Natchpai/LQRx_InterleavedBuck/Images/GCM155R71H104KE02J-100nF50V.png

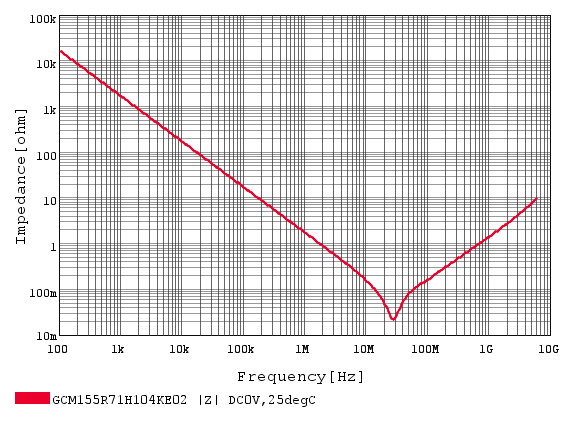
Images/GCM155R71H104KE02J-100nF50V.png
