Natchpai/LQRx_InterleavedBuck/Images/GRM21BZ71E475KE15L-4u7F25V-Derating.png

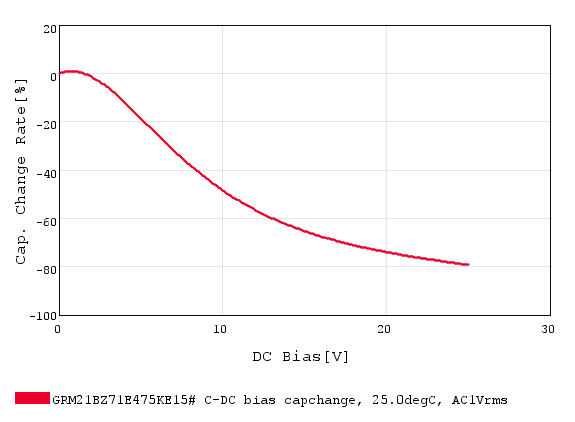
Images/GRM21BZ71E475KE15L-4u7F25V-Derating.png
