Natchpai/LQRx_InterleavedBuck/Images/GRM31CR71H475KA12L-4u7F50V_Z.png

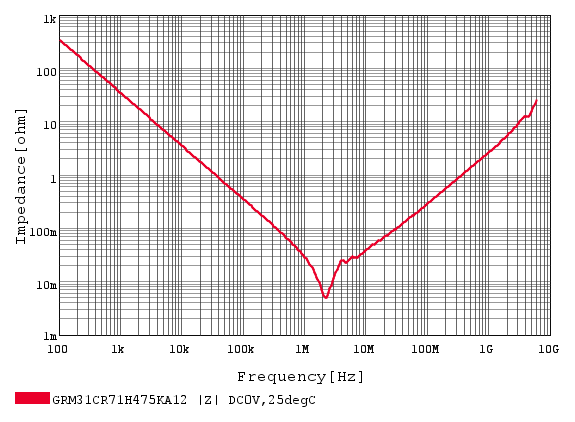
Images/GRM31CR71H475KA12L-4u7F50V_Z.png
