Natchpai/LQRx_InterleavedBuck/Images/GRM155R71E103KA01D.png

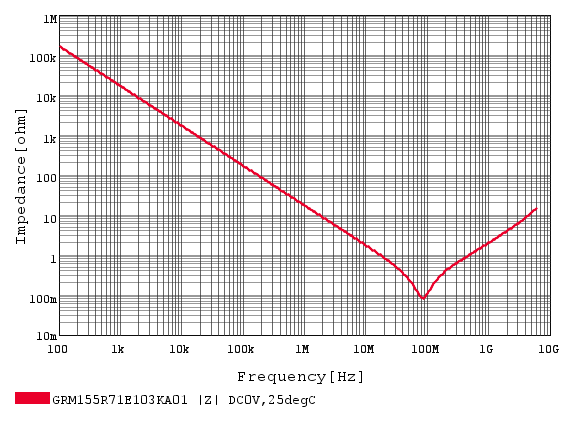
Images/GRM155R71E103KA01D.png
