Natchpai/LQRx_InterleavedBuck/Images/Render-Board/2Phase_SynchBuck_Bottomview_v1-1 (Large).png

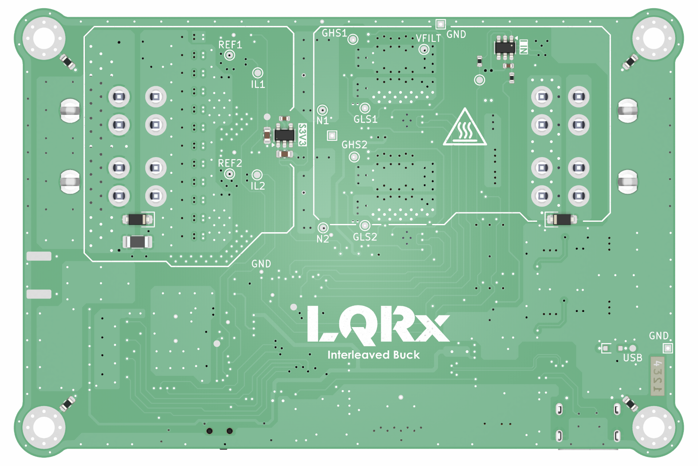
Images/Render-Board/2Phase_SynchBuck_Bottomview_v1-1 (Large).png
