Natchpai/LQRx_InterleavedBuck/Simulation/LC_Filter.asc

C1: cap; {Cd}
C2: cap; {Cf}
C3: cap; 0.1µ
C4: cap; {Cf}
C5: cap; 0.1µ
C6: cap; 10p
C7: cap; 10p
C8: cap; {Cd}
C9: cap; 2µ
C10: cap; {Cd}
C11: cap; 0.1µ
C12: cap; 0.1µ
C13: cap; 10p
C14: cap; 10p
C15: cap; {Cd}
C16: cap; 2µ
C17: cap; {Cd}
C18: cap; {Cf}
C19: cap; 0.1µ
C20: cap; 0.1µ
C21: cap; 10p
C22: cap; 10p
C23: cap; {Cf}
C24: cap; {Ci}; Lser=200p
C25: cap; 47µ; Rser=10m Lser=2n
C26: cap; 47µ
C27: cap; 47µ; Rser=10m Lser=2n
C28: cap; {Ci}; Lser=200p
C29: cap; {Ci}; Lser=200p
C30: cap; {Ci}; Lser=200p
C31: cap; {Ci}; Lser=200p
C32: cap; {Ci}; Lser=200p
C33: cap; 0.1µ; Lser=200p
C34: cap; 0.1µ; Lser=200p
C35: cap; {Ci}; Lser=200p
C36: cap; 47µ; Lser=3n
C37: cap; 47µ; Lser=3n
C38: cap; 47µ; Lser=3n
C39: cap; 0.1µ; Lser=200p
C40: cap; 0.1µ; Lser=200p
C41: cap; {Ci}; Lser=200p
C42: cap; {Ci}; Lser=200p
C43: cap; {Ci}; Lser=200p
C44: cap; {Ci}; Lser=200p
C45: cap; {Ci}; Lser=200p
C46: cap; {Ci}; Lser=200p
C47: cap; {Ci}; Lser=200p
C48: cap; {Ci}; Lser=200p
C49: cap; {Ci}; Lser=200p
C50: cap; 47µ; Lser=3n
C51: cap; 47µ; Lser=3n
C52: cap; 47µ; Lser=3n
C53: cap; 0.1µ; Lser=200p
C54: cap; 0.1µ; Lser=200p
C55: cap; {Ci}; Lser=200p
C56: cap; {Ci}; Lser=200p
C57: cap; {Ci}; Lser=200p
C58: cap; {Ci}; Lser=200p
C59: cap; {Ci}; Lser=200p
C60: cap; {Ci}; Lser=200p
C61: cap; {Ci}; Lser=200p
C62: cap; {Ci}; Lser=200p
C63: cap; {Ci}; Lser=200p
C64: cap; {Ci}; Lser=200p
C65: cap; {Ci}; Lser=200p
C66: cap; {Ci}; Lser=200p
C67: cap; {Ci}; Lser=200p
C68: cap; {Ci}; Lser=200p
I1: current; ""; AC 1
I2: current; ""; AC 1
I3: current; ""; AC 1
I4: current; ""; AC 1
L1: ind; 1µ; Rser=1m
L2: ind; 1µ; Rser=1m
L3: ind; 250p; Rser=1m
L4: ind; 250p; Rser=1m
L5: ind; 5n; Rser=1m
L6: ind; 250p; Rser=1m
L7: ind; 250p; Rser=1m
L8: ind; 1µ; Rser=1m
L9: ind; 1µ; Rser=1m
L10: ind; 5n; Rser=1m
L11: ind; 250p; Rser=1m
L12: ind; 1µ; Rser=1m
L13: ind; 250p; Rser=1m
L14: ind; 250p; Rser=1m
L15: ind; 5n; Rser=1m
L16: ind; 1µ; Rser=1m
L17: ind; 5n; Rser=1m
L18: ind; 5n; Rser=1m
L19: ind; 250p; Rser=1m
L20: ind; 250p; Rser=1m
L21: ind; 250p; Rser=1m
L22: ind; 250p; Rser=1m
L23: ind; 250p; Rser=1m
L24: ind; 1µ; Rser=1m
L25: ind; 1µ; Rser=1m
L26: ind; 1µ; Rser=1m
R1: res; 6m
R2: res; {Rd}
R3: res; 2m
R4: res; 6m
R5: res; 0.01
R6: res; 2m
R7: res; 0.01
R8: res; 6m
R9: res; 6m
R10: res; 2m
R11: res; 6m
R12: res; 2m
R13: res; 0.01
R14: res; 0.01
R15: res; {Zin}
R16: res; {Rd}
R17: res; {Rd}
R18: res; {Rd}
R19: res; {Rd}
R20: res; 6m
R21: res; 2m
R22: res; 0.01
R23: res; 0.01
R24: res; 2m
R25: res; 0.4
R26: res; 4m
R27: res; 0.5
R28: res; 5.6m
R29: res; 5m
R30: res; 0.4
R31: res; 1m
R32: res; 1m
R33: res; 1m
R34: res; 1m
R35: res; 4m
R36: res; 4m
R37: res; 4m
R38: res; 1m
R39: res; 1m
R40: res; 4m
R41: res; 4m
R42: res; 2m
R43: res; 2m
R44: res; 0.4
R45: res; 4m
R46: res; 0.4
R47: res; 5.6m
R48: res; 5m
R49: res; 0.4
R50: res; 1m
R51: res; 1m
R52: res; 1m
R53: res; 1m
R54: res; 4m
R55: res; 4m
R56: res; 4m
R57: res; 1m
R58: res; 1m
R59: res; 4m
R60: res; 4m
R61: res; 2m
R62: res; 2m
R63: res; 4m
R64: res; 4m
R65: res; 4m
R66: res; 4m
R67: res; 0.4
R68: res; 0.4
R69: res; 5.6m
R71: res; 0.4
R72: res; 1m
R73: res; 1m
R74: res; 1m
R75: res; 1m
R76: res; 1m
R77: res; 1m
R78: res; 2m
R79: res; 2m
R80: res; 4m
R81: res; 4m
R82: res; 4m
R83: res; 4m
R84: res; 4m
R85: res; 4m
R86: res; 4m
R87: res; 4m
R88: res; 4m
R89: res; 4m
R90: res; 4m
R91: res; 4m
R92: res; 4m
R93: res; 4m
R94: res; 100µ
R95: res; 100µ
R96: res; 100µ
V1: voltage; ""; AC 1
V2: voltage; ""; AC 1
V3: voltage; ""; AC 1
V4: voltage; ""; AC 1
V5: voltage; ""; AC 1
V6: voltage; ""; AC 1
Named nets: 0, Z1, Z2, in3, in4, Zin, out1, out2
.ac dec 100 100 101meg
.param Zin = {12/I}/({d*d})
.param I=20
.param d=0.5
.param Cd=47u
.param Rd=0.39
.param Cf=24u
.param Ci=3.3u
