Natchpai/LQRx_InterleavedBuck/Simulation/buck.asc

C1: cap; 3µ; Lser=200p
C2: cap; 47µ; Rser=10m Lser=2n
C3: cap; 47µ
C4: cap; 47µ; Rser=10m Lser=2n
C5: cap; 47µ
C6: cap; 3µ; Lser=200p
C7: cap; 3µ; Lser=200p
C8: cap; 3µ; Lser=200p
C9: cap; 3µ; Lser=200p
C10: cap; 3µ; Lser=200p
C11: cap; 0.1µ; Lser=200n
C12: cap; 0.1µ; Lser=200p
C13: cap; 94µ
C14: cap; 3µ; Lser=200p
C15: cap; 3µ; Lser=200p
C16: cap; 470µ
C17: cap; 10p
C18: cap; 10p
C19: cap; 50p; Lser=1m
C20: cap; 50p; Rser=1m
C21: cap; 200p
C22: cap; 200p
D1: diode; MBRB2545CT
D2: diode; MBRB2545CT
L1: ind; 1µ; Rser=1m
L2: ind; 10µ; Rser=1m
L3: ind; 10µ; Rser=1m
L4: ind; 100p; Rser=1m
L5: ind; 50n; Rser=1m
L6: ind; 100p; Rser=1m
L7: ind; 2n; Rser=1m
L8: ind; 2n; Rser=1m
M1: nmos; BSB012N03LX3
M2: nmos; BSB012N03LX3
R1: res; 15m
R2: res; 0.39
R3: res; 4m
R4: res; 0.5
R5: res; 5.6m
R6: res; 5m
R7: res; 0.39
R8: res; 2m
R9: res; 0.75
R10: res; 100µ
R11: res; 15m
R12: res; 100µ
R13: res; 4.5
R14: res; 4.5
R15: res; 4m
R16: res; 4m
R17: res; 4m
R18: res; 1m
R19: res; 1m
R20: res; 4m
R21: res; 4m
R22: res; 2m
R23: res; 2m
R24: res; 2
R25: res; 2
R26: res; R=if(time>1m,0.75,10)
R27: res; 20m
R28: res; 4m
R29: res; 4m
R30: res; 5m
R31: res; 2
V1: voltage; PULSE(0 9 0.2m 10n 10n 2.6u 5u)
V2: voltage; 30
V3: voltage; PULSE(0 9 202.5u 10n 10n 2.6u 5u)
Named nets: 0, out, in
.tran 2m
.meas TRAN ICrms_val2 RMS I(C2) FROM 1.8m TO 2m
.meas TRAN ICrms_val1 RMS I(C2) FROM 0.4m TO 0.8m
.meas Pout AVG V(out)*I(R26) FROM 1.8m TO 2m
.meas Pin AVG V(in)*I(V2) FROM 1.8m TO 2m
.meas Eff param Pout/Pin
