Natchpai/LQRx_InterleavedBuck/Simulation/LC_filter_supplies.asc

C1: cap; {C}; Lser=200p
C2: cap; {C}; Rser=0.01 Lser=200p
C3: cap; {C}; Rser=0.01 Lser=200p
C4: cap; {C}; Lser=200p
C5: cap; {C}; Rser=0.01 Lser=200p
C6: cap; {Cd}; Lser=200p
C8: cap; {Cd}; Lser=200p
C9: cap; {Cd}; Lser=200p
C10: cap; {C}; Rser=0.01 Lser=200p
I1: current; ""; AC 1
I2: current; ""; AC 1
I3: current; ""; AC 1
L1: ind; {L}; Rser=0
L2: ind; {L}; Rser=0
L3: ind; {L}; Rser=0
L4: ind; {L}; Rser=0
L6: ind; {L}; Rser=0
R1: res; {Rd}
R2: res; {RL}
R3: res; 0.01
R4: res; 0.01
R5: res; {RL}
R6: res; 0.01
R7: res; {RL}
R8: res; 8
R9: res; 0.01
R10: res; {Rd}
R11: res; {RL}
R13: res; 0.01
R15: res; 0.5
R16: res; {RL}
R17: res; 0.01
V1: voltage; ""; AC 1
V2: voltage; ""; AC 1
V4: voltage; ""; AC 1
Named nets: 0, 1, 2, o1, o2
.ac dec 100 1k 100meg
.param L=2.2u
.param C = 3u
.param RL=0.2
.param Cd=15u
.param Rd=1
